Cipulot/EC-Pro-2/PCB/EC_Pro2_Mainboard/EC_Pro2_Mainboard.kicad_sch

## KiCad design PCB/EC_Pro2_Mainboard/EC_Pro2_Mainboard.kicad_sch (2024-06-05)

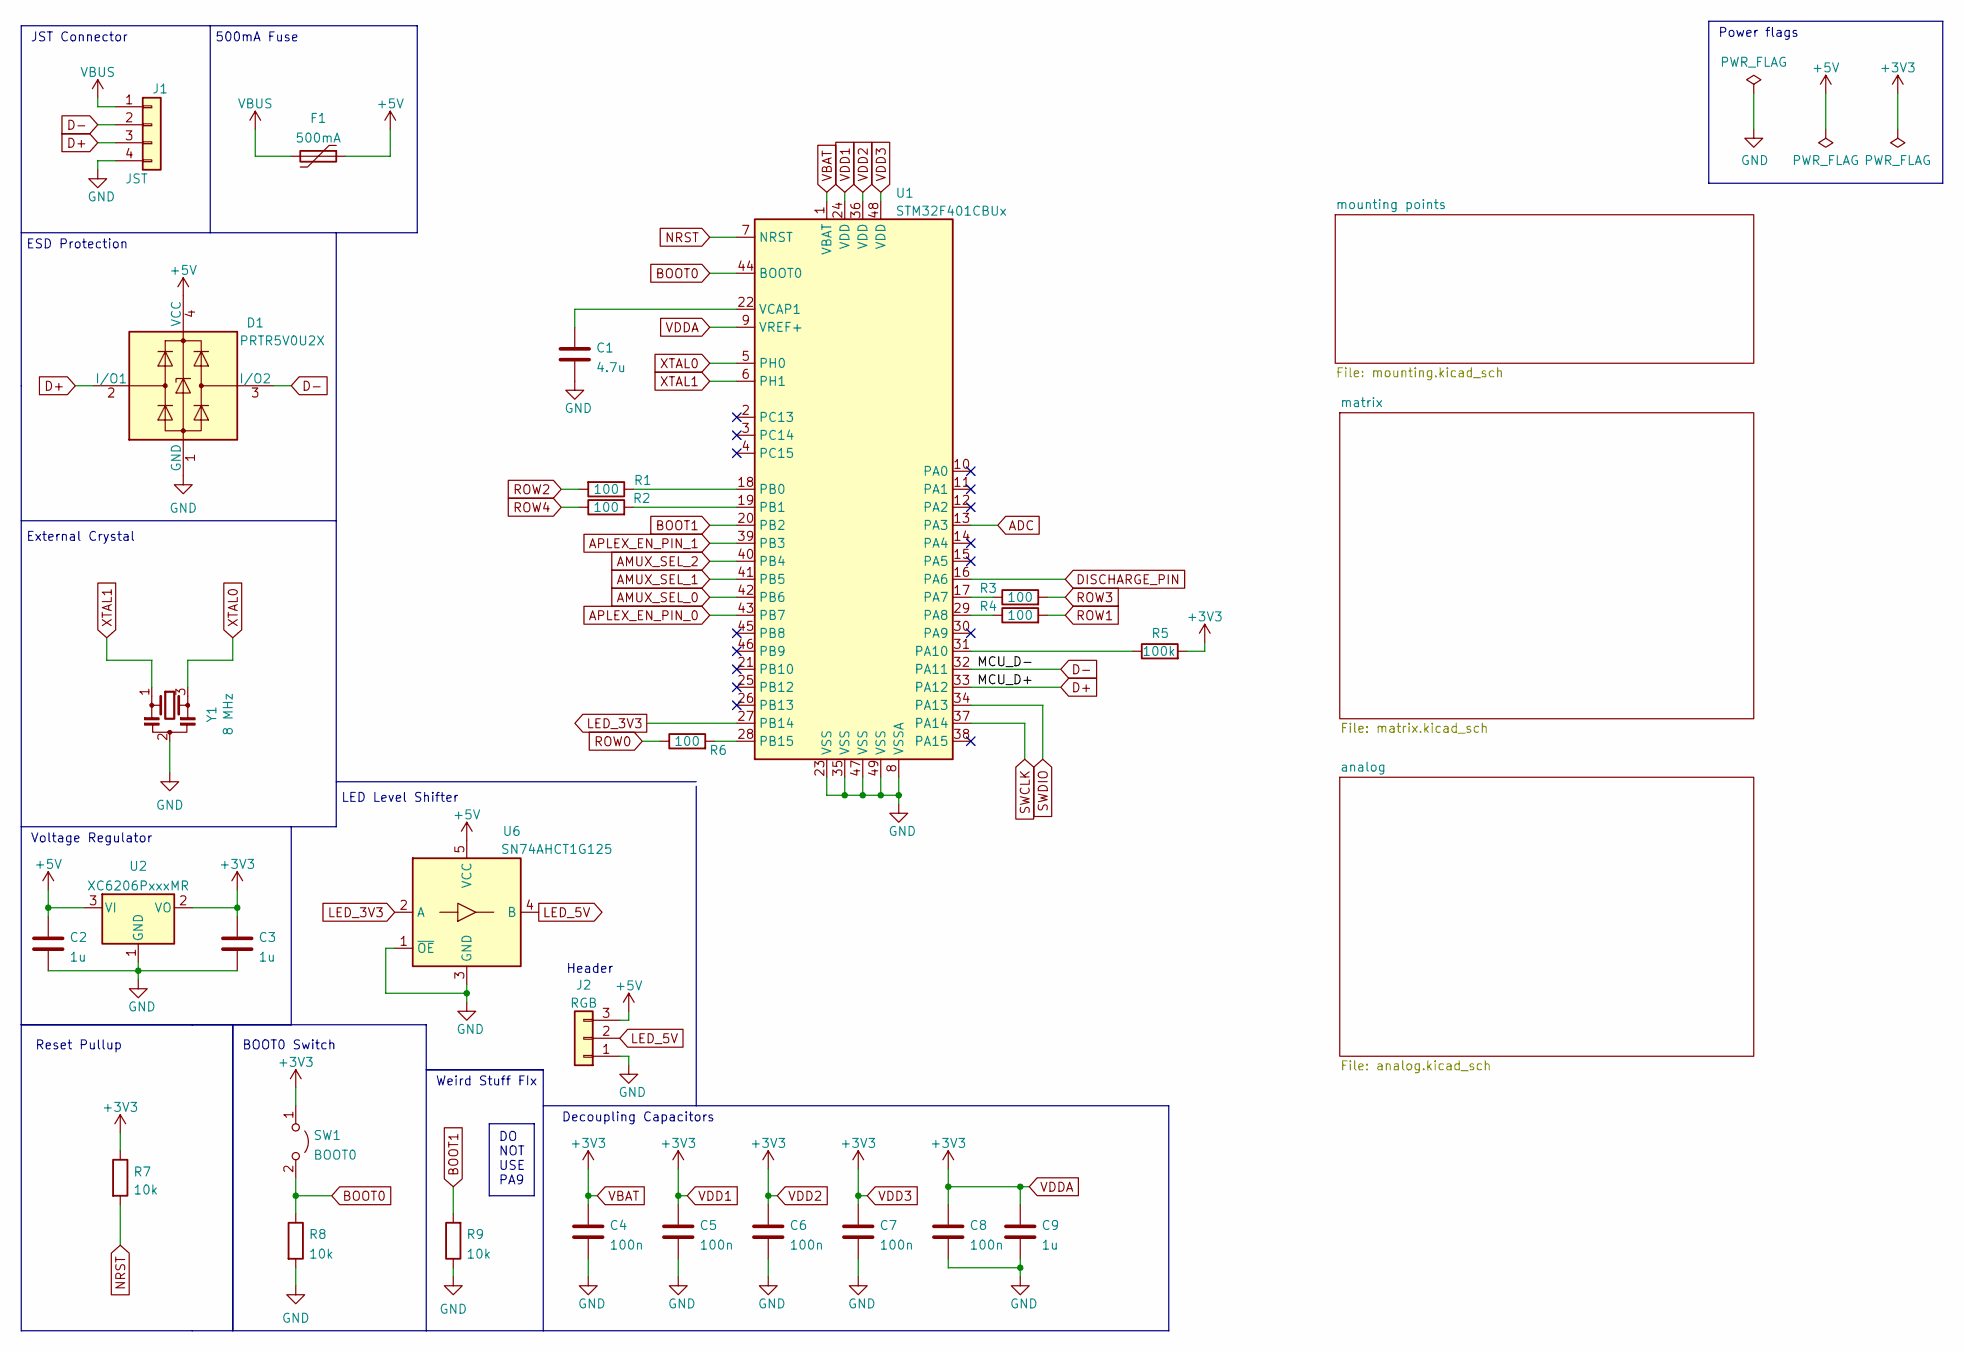
[picture p16: schematic EC_Pro2_Mainboard.kicad_sch]

Parts:
C1: 4.7u; C_0402_1005Metric; LCSC C23733
C2, C3, C9: 1u; C_0402_1005Metric; LCSC C52923
C4, C5, C6, C7, C8: 100n; C_0402_1005Metric; LCSC C307331
D1: PRTR5V0U2X; SOT-143; LCSC C2827688
F1: 500mA; Fuse_1206_3216Metric; LCSC C70076
J1: JST; JST-SR-4; LCSC C145956
J2: RGB; PinSocket_1x03_P2.54mm_Vertical
R1, R2, R3, R4, R6: 100; R_0402_1005Metric; LCSC C25076
R5: 100k; R_0402_1005Metric; LCSC C25741
R7, R8, R9: 10k; R_0402_1005Metric; LCSC C25744
SW1: BOOT0; PinHeader_1x02_P2.54mm_Vertical
U1: STM32F401CBUx; QFN-48-1EP_7x7mm_P0.5mm_EP5.6x5.6mm; LCSC C118825
U2: XC6206PxxxMR; SOT-23; LCSC C5446
U6: SN74AHCT1G125; SOT-23-5; LCSC C7484
Y1: 8 MHz; Resonator_SMD_Murata_CSTxExxV-3Pin_3.0x1.1mm; LCSC C907975

Connections:
+3V3: C3.1, C4.1, C5.1, C6.1, C7.1, C8.1, C9.1, R5.2, R7.1, SW1.1 (A), U1.1 (VBAT), U1.9 (VREF+), U1.24 (VDD), U1.36 (VDD), U1.48 (VDD), U2.2 (VO)
+5V: C2.1, D1.4 (VCC), F1.1, J2.3, U2.3 (VI), U6.5 (VCC)
ADC: U1.13 (PA3)
AMUX_SEL_0: U1.42 (PB6)
AMUX_SEL_1: U1.41 (PB5)
AMUX_SEL_2: U1.40 (PB4)
APLEX_EN_PIN_0: U1.43 (PB7)
APLEX_EN_PIN_1: U1.39 (PB3)
BOOT0: R8.1, SW1.2 (B), U1.44 (BOOT0)
BOOT1: R9.2, U1.20 (PB2)
D+: D1.2 (I/O1), J1.3, U1.33 (PA12)
D-: D1.3 (I/O2), J1.2, U1.32 (PA11)
DISCHARGE_PIN: U1.16 (PA6)
GND: C1.2, C2.2, C3.2, C4.2, C5.2, C6.2, C7.2, C8.2, C9.2, D1.1 (GND), J1.4, J2.1, R8.2, R9.1, U1.8 (VSSA), U1.23 (VSS), U1.35 (VSS), U1.47 (VSS), U1.49 (VSS), U2.1 (GND), U6.1 (~OE), U6.3 (GND), Y1.2
LED_3V3: U1.27 (PB14), U6.2 (A)
LED_5V: J2.2, U6.4 (B)
NRST: R7.2, U1.7 (NRST)
unnamed: C1.1, U1.22 (VCAP1)
unnamed: R1.1, U1.18 (PB0)
unnamed: R2.2, U1.19 (PB1)
unnamed: R3.1, U1.17 (PA7)
unnamed: R4.1, U1.29 (PA8)
unnamed: R5.1, U1.31 (PA10)
unnamed: R6.2, U1.28 (PB15)
ROW0: R6.1
ROW1: R4.2
ROW2: R1.2
ROW3: R3.2
ROW4: R2.1
SWCLK: U1.37 (PA14)
SWDIO: U1.34 (PA13)
VBUS: F1.2, J1.1
XTAL0: U1.5 (PH0), Y1.3
XTAL1: U1.6 (PH1), Y1.1

Notes on the sheet:
DO NOT USE PA9
Voltage Regulator
JST Connector
Header
BOOT0 Switch
External Crystal
500mA Fuse
Weird Stuff FIx
Decoupling Capacitors
Power flags
LED Level Shifter
ESD Protection
Reset Pullup
