Cipulot/EC-Pro-2/PCB/EC_Pro2_Mainboard/analog.kicad_sch

## KiCad design PCB/EC_Pro2_Mainboard/analog.kicad_sch (2024-06-05)

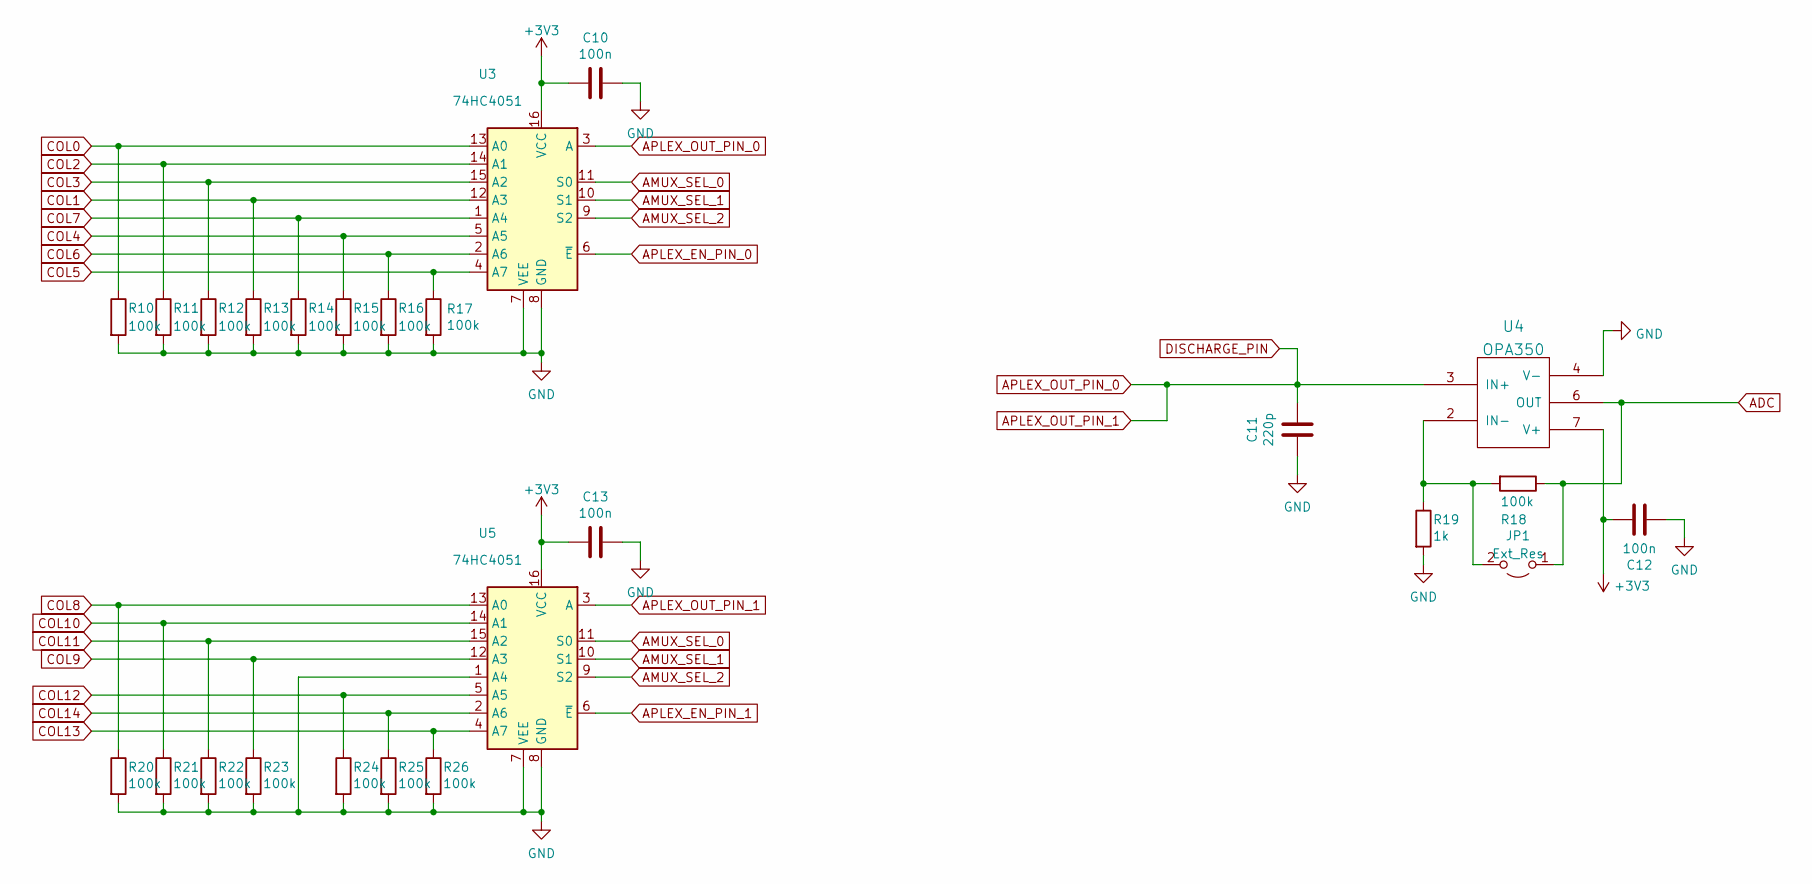
[picture p17: schematic analog.kicad_sch]

Parts:
C10, C12, C13: 100n; C_0402_1005Metric; LCSC C307331
C11: 220p; C_0402_1005Metric; LCSC C1530
JP1: Ext_Res; R_0603_1608Metric_Pad0.98x0.95mm_HandSolder
R10, R11, R12, R13, R14, R15, R16, R17, R18, R20, R21, R22, R23, R24, R25, R26: 100k; R_0402_1005Metric; LCSC C25741
R19: 1k; R_0402_1005Metric; LCSC C11702
U3, U5: 74HC4051; TSSOP16; LCSC C5645
U4: OPA350; SOIC-8_3.9x4.9mm_P1.27mm; LCSC C13388

Connections:
+3V3: C10.2, C12.2, C13.2, U3.16 (VCC), U4.7 (V+), U5.16 (VCC)
ADC: JP1.1 (A), R18.1, U4.6 (OUT)
AMUX_SEL_0: U3.11 (S0), U5.11 (S0)
AMUX_SEL_1: U3.10 (S1), U5.10 (S1)
AMUX_SEL_2: U3.9 (S2), U5.9 (S2)
APLEX_EN_PIN_0: U3.6 (~E)
APLEX_EN_PIN_1: U5.6 (~E)
APLEX_OUT_PIN_0: C11.1, U3.3 (A), U4.3 (IN+), U5.3 (A)
COL0: R10.1, U3.13 (A0)
COL1: R13.1, U3.12 (A3)
COL2: R11.1, U3.14 (A1)
COL3: R12.1, U3.15 (A2)
COL4: R15.1, U3.5 (A5)
COL5: R17.1, U3.4 (A7)
COL6: R16.1, U3.2 (A6)
COL7: R14.1, U3.1 (A4)
COL8: R20.1, U5.13 (A0)
COL9: R23.1, U5.12 (A3)
COL10: R21.1, U5.14 (A1)
COL11: R22.1, U5.15 (A2)
COL12: R24.1, U5.5 (A5)
COL13: R26.1, U5.4 (A7)
COL14: R25.1, U5.2 (A6)
GND: C10.1, C11.2, C12.1, C13.1, R10.2, R11.2, R12.2, R13.2, R14.2, R15.2, R16.2, R17.2, R19.2, R20.2, R21.2, R22.2, R23.2, R24.2, R25.2, R26.2, U3.7 (VEE), U3.8 (GND), U4.4 (V-), U5.1 (A4), U5.7 (VEE), U5.8 (GND)
unnamed: JP1.2 (B), R18.2, R19.1, U4.2 (IN-)
