Cipulot/EC-Pro-2/PCB/EC_Pro2_Mainboard/mounting.kicad_sch

## KiCad design PCB/EC_Pro2_Mainboard/mounting.kicad_sch (2024-06-05)

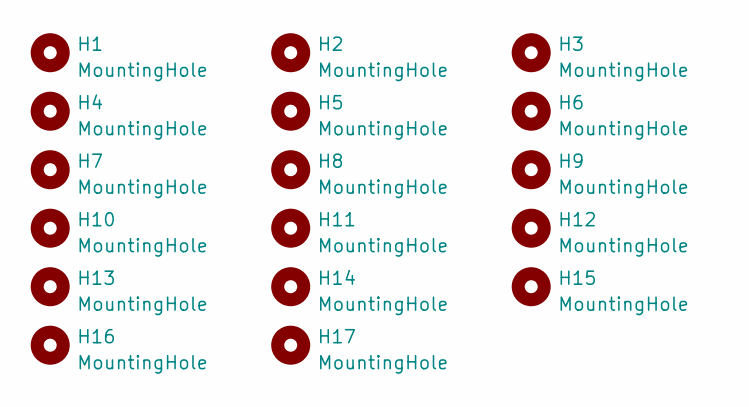
[picture p19: schematic mounting.kicad_sch]

Parts:
H1, H2, H3, H4, H5, H6, H7, H8, H9, H10, H11, H12, H13, H14, H15, H16, H17: MountingHole; HOLE_M2
